serge-scl/braslet/design CAD/cup04.FCStd

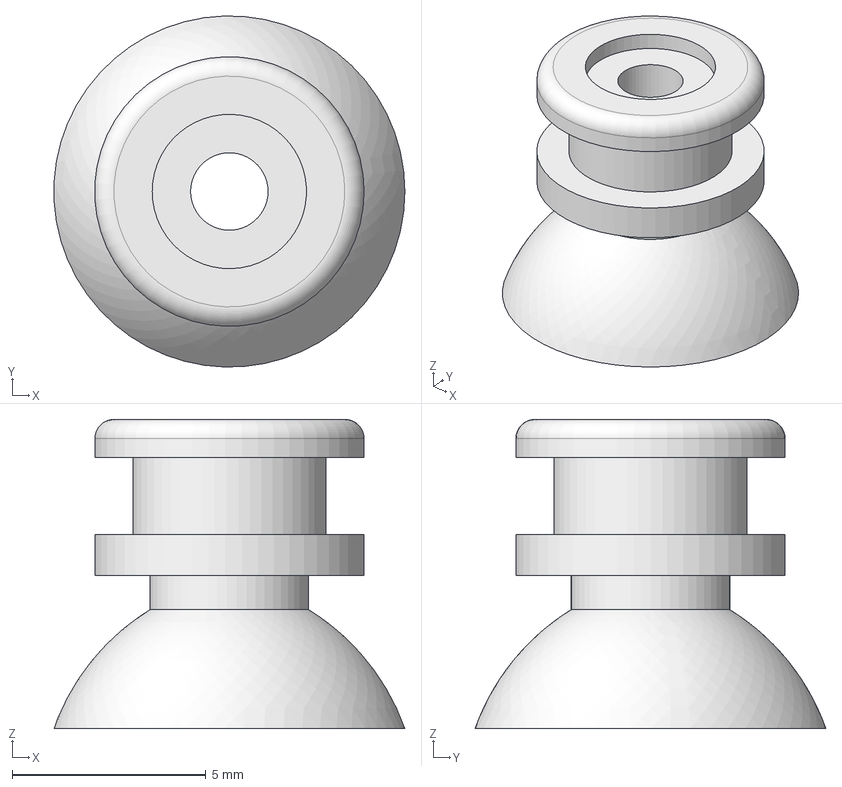
[picture p15: CAD file, 2022-11-26]
design CAD/cup04.FCStd
9.07 x 9.07 x 7.99 mm
