serge-scl/braslet/design CAD/sub_assembly/claster_feed_ring03.FCStd

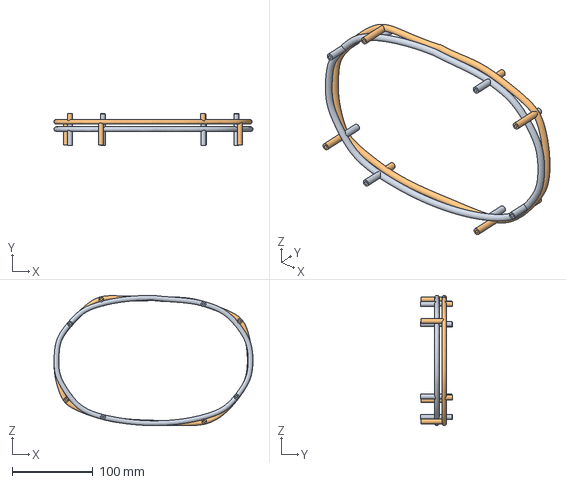
[picture p16: CAD file, 2022-08-05]
design CAD/sub_assembly/claster_feed_ring03.FCStd
246.3 x 39.1 x 161.5 mm
pip_feed_ring05_001
pip_feed_ring06_001
