serge-scl/braslet/design CAD/btm_spr_modl_sh03.FCStd

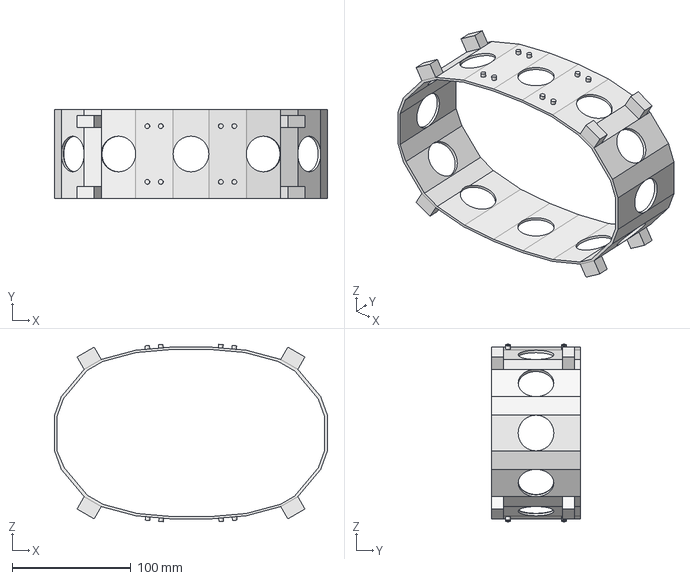
[picture p17: CAD file, 2022-10-20]
design CAD/btm_spr_modl_sh03.FCStd
230.0 x 75.0 x 149.6 mm
