serge-scl/braslet/design CAD/sub_assembly/con_spring_pip_sct01.FCStd

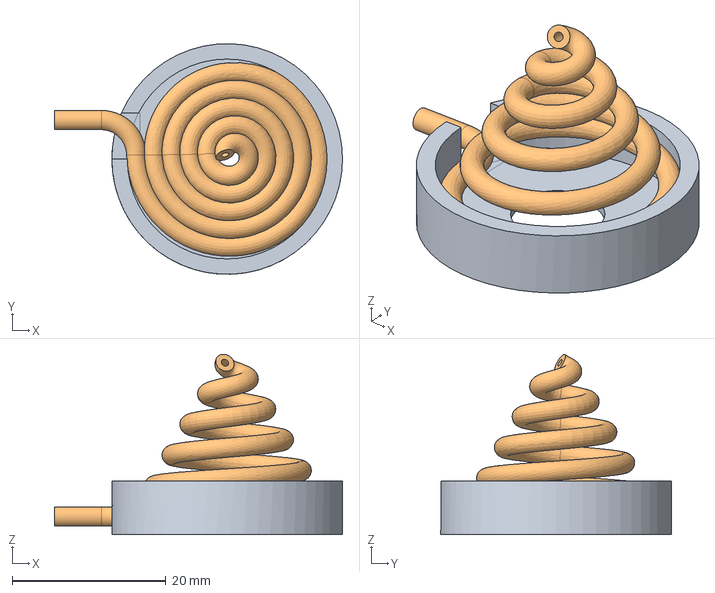
[picture p18: CAD file, 2022-07-16]
design CAD/sub_assembly/con_spring_pip_sct01.FCStd
37.5 x 30.0 x 23.5 mm
con_pip_spring_sokt01_001
con_spring_plp01_001
