serge-scl/braslet/design CAD/pip_feed_ring05.FCStd

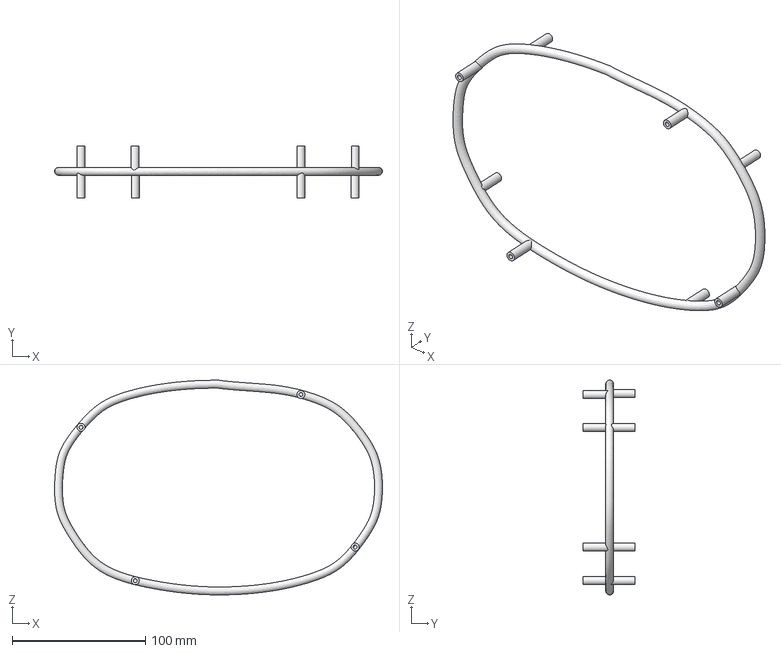
[picture p19: CAD file, 2022-08-05]
design CAD/pip_feed_ring05.FCStd
246.3 x 39.0 x 161.3 mm
