serge-scl/braslet/design CAD/sub_assembly/con_spring_sens_sct01.FCStd

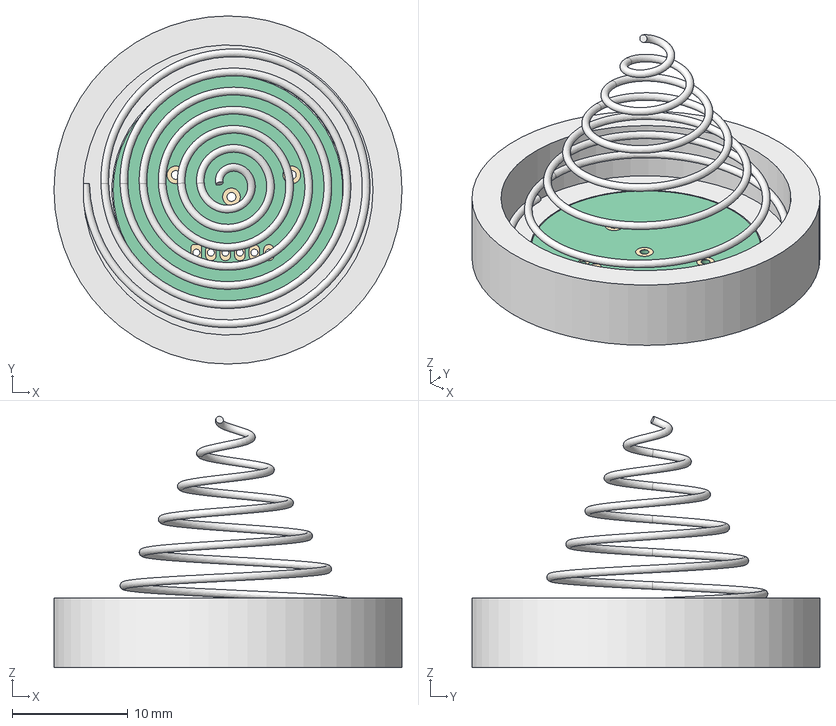
[picture p20: CAD file, 2022-07-15]
design CAD/sub_assembly/con_spring_sens_sct01.FCStd
30.0 x 30.0 x 21.7 mm
con_spring_sockt01_001
con_spring_stl01_001
Pcb_2f88
topPads_2f88
botPads_2f88
