serge-scl/braslet/design CAD/sub_assembly/solenoid_in_chamb01.FCStd

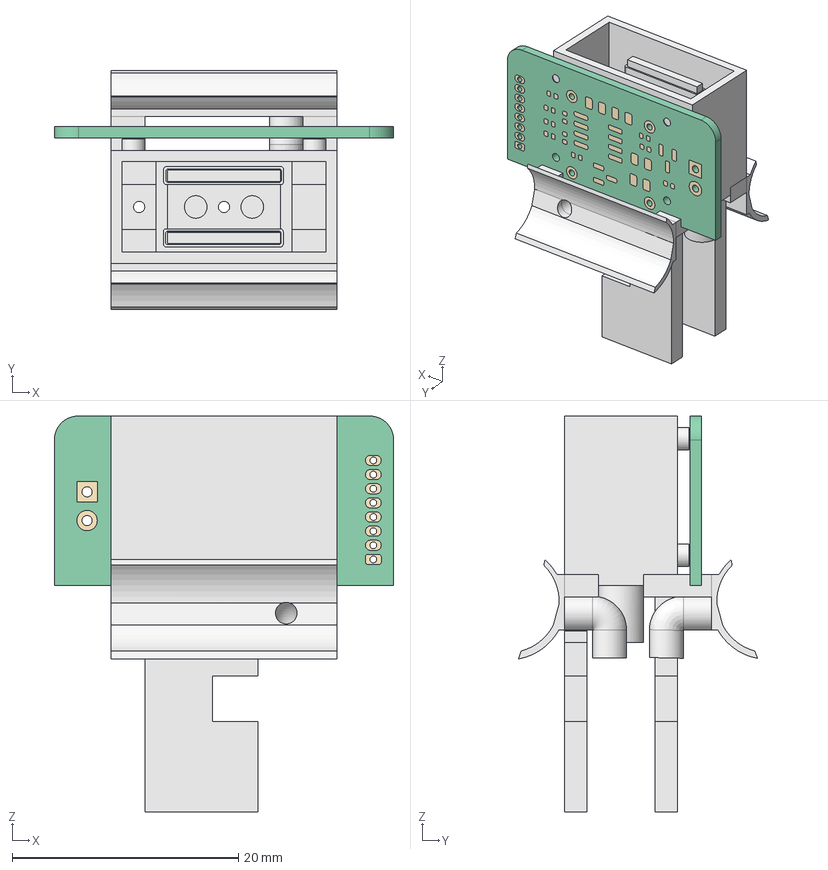
[picture p21: CAD file, 2022-07-13]
design CAD/sub_assembly/solenoid_in_chamb01.FCStd
30.0 x 21.1 x 35.0 mm
shell_chamb12_001
el_magnetcore03_001
magn_coil03_Body_001
magn_coil03_Body_002
Pcb_b2f7
topPads_b2f7
botPads_b2f7
actuator8_pistonPCBside_001
actuator8_piston_001
