serge-scl/braslet/design CAD/lips02.FCStd

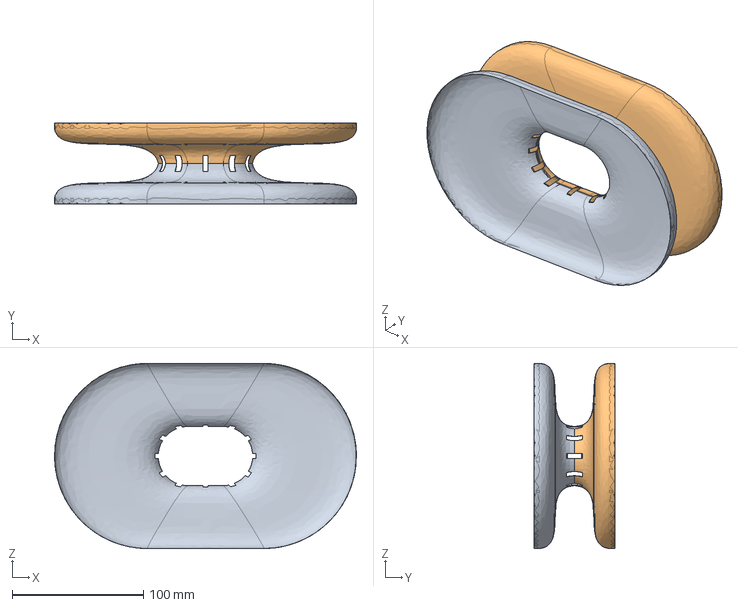
[picture p22: CAD file, 2022-07-19]
design CAD/lips02.FCStd
230.3 x 62.0 x 141.2 mm
Extrusion (Mirror #1)
