serge-scl/braslet/design CAD/sub_assembly/Ring_pneum_act01.FCStd

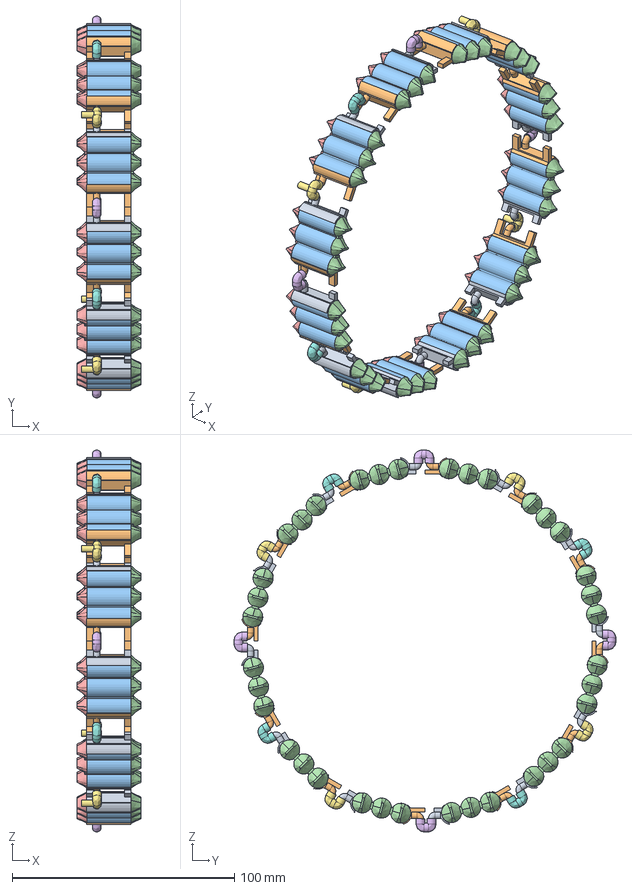
[picture p23: CAD file, 2022-05-03]
design CAD/sub_assembly/Ring_pneum_act01.FCStd
29.0 x 171.8 x 171.8 mm
