serge-scl/braslet/design CAD/con_pip_spring_sokt01.FCStd

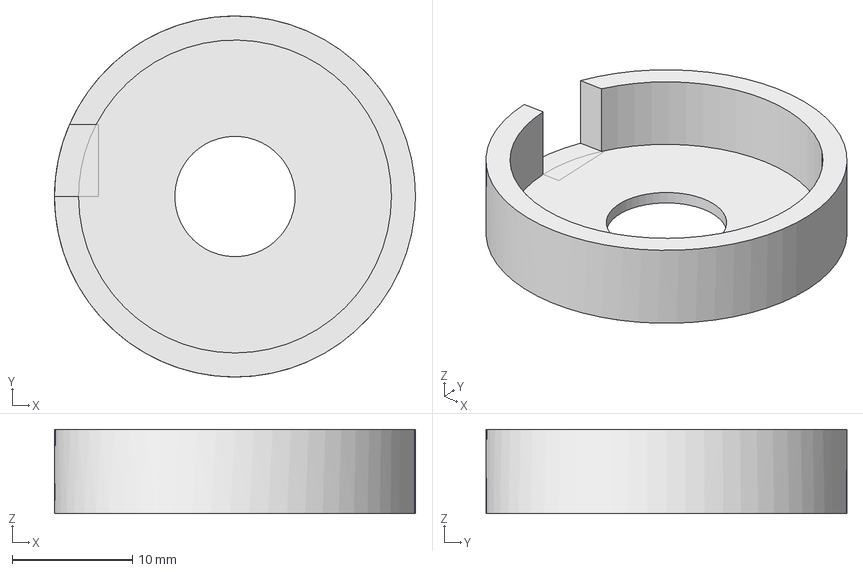
[picture p24: CAD file, 2022-07-16]
design CAD/con_pip_spring_sokt01.FCStd
30.0 x 30.0 x 7.00 mm
