serge-scl/braslet/design CAD/sub_assembly/ring_vacuum_line01.FCStd

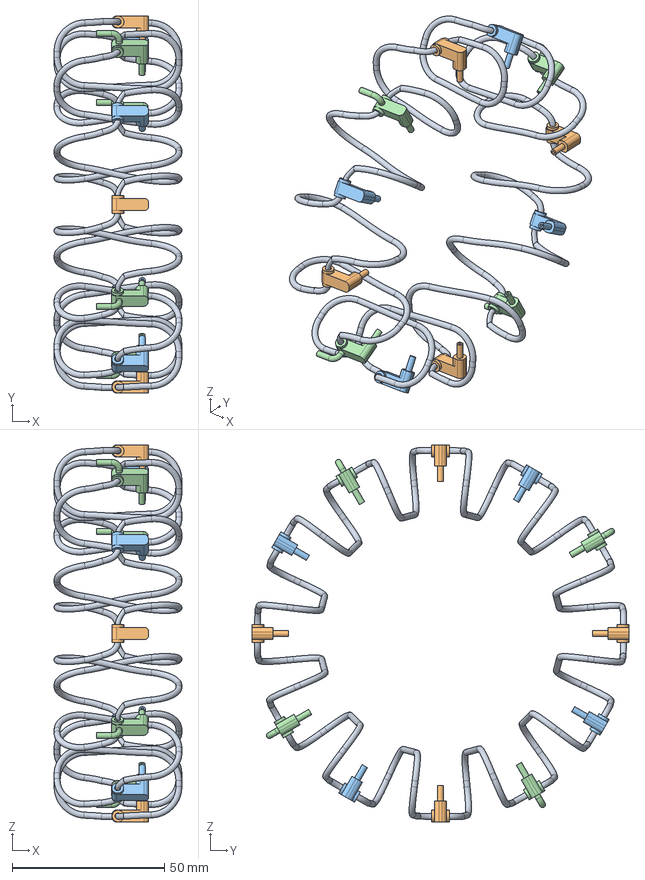
[picture p25: CAD file, 2022-04-30]
design CAD/sub_assembly/ring_vacuum_line01.FCStd
42.0 x 123.9 x 123.9 mm
