serge-scl/braslet/design CAD/con_spring_sockt01.FCStd

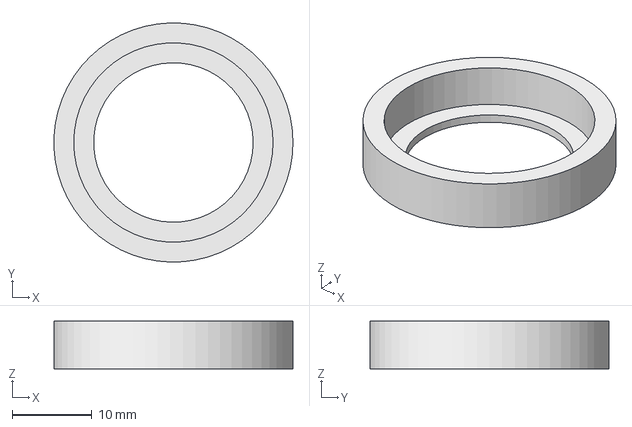
[picture p26: CAD file, 2022-07-15]
design CAD/con_spring_sockt01.FCStd
30.0 x 30.0 x 6.00 mm
