serge-scl/braslet/design CAD/con_spring_plp01.FCStd

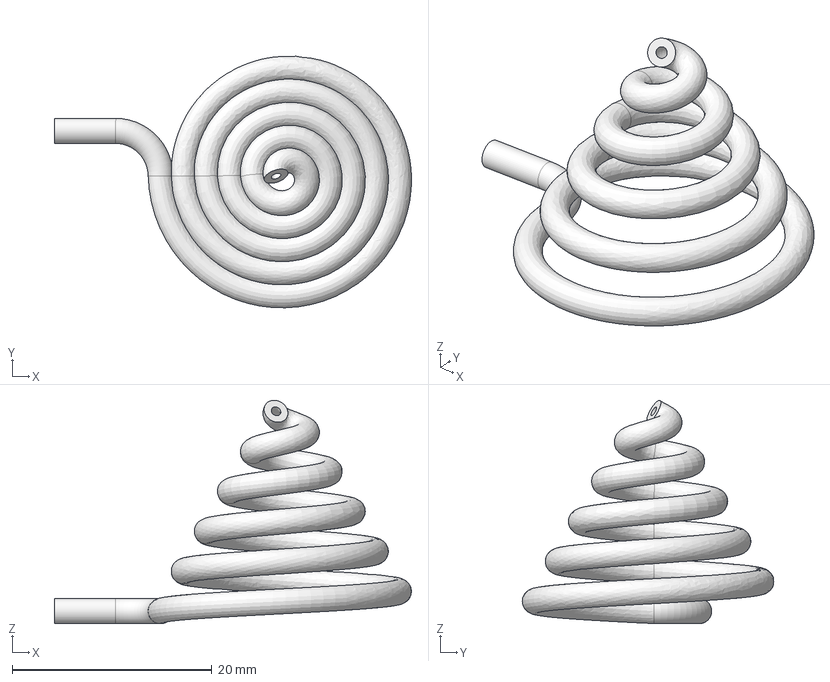
[picture p27: CAD file, 2022-07-13]
design CAD/con_spring_plp01.FCStd
35.7 x 25.2 x 22.3 mm
