serge-scl/braslet/design CAD/con_spring_stl01.FCStd

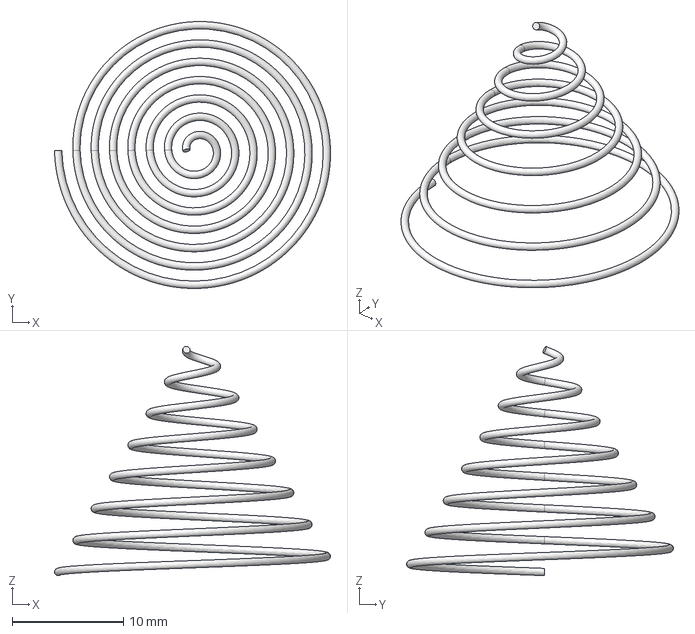
[picture p28: CAD file, 2022-07-13]
design CAD/con_spring_stl01.FCStd
24.8 x 24.0 x 20.6 mm
