serge-scl/braslet/design CAD/top_spr_modl_shell01.FCStd

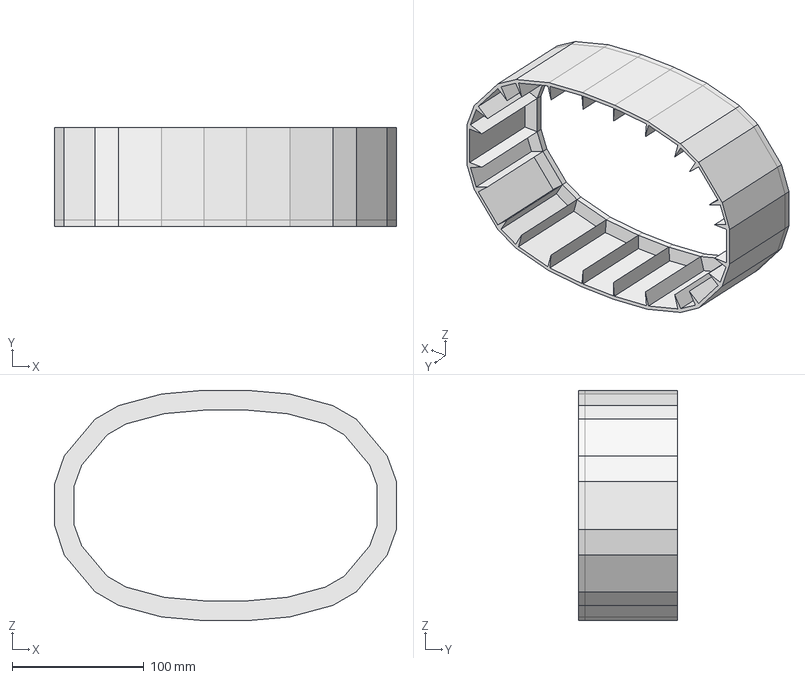
[picture p29: CAD file, 2022-07-08]
design CAD/top_spr_modl_shell01.FCStd
259.6 x 75.0 x 175.0 mm
