serge-scl/braslet/design CAD/coil_pins02.FCStd

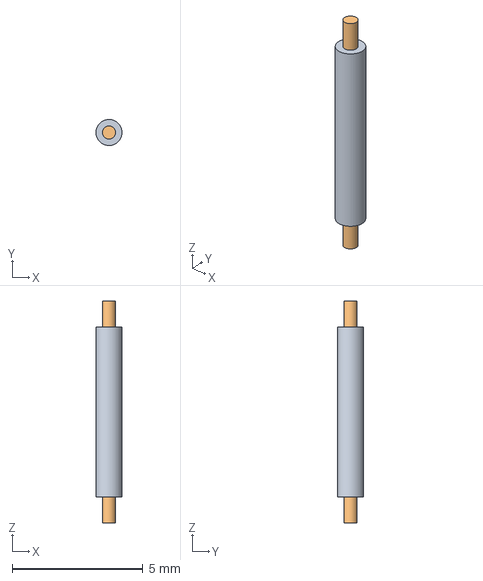
[picture p30: CAD file, 2022-05-10]
design CAD/coil_pins02.FCStd
0.999 x 1 x 8.50 mm
Tube
