serge-scl/braslet/design CAD/coil_pins01.FCStd

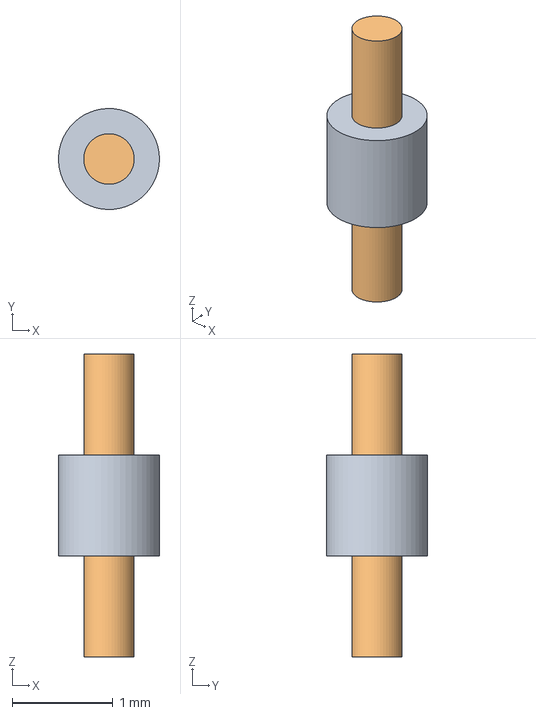
[picture p31: CAD file, 2022-05-10]
design CAD/coil_pins01.FCStd
0.999 x 1 x 3.00 mm
Tube
