serge-scl/braslet/design CAD/branch_pipe_tee0_feeder01.FCStd

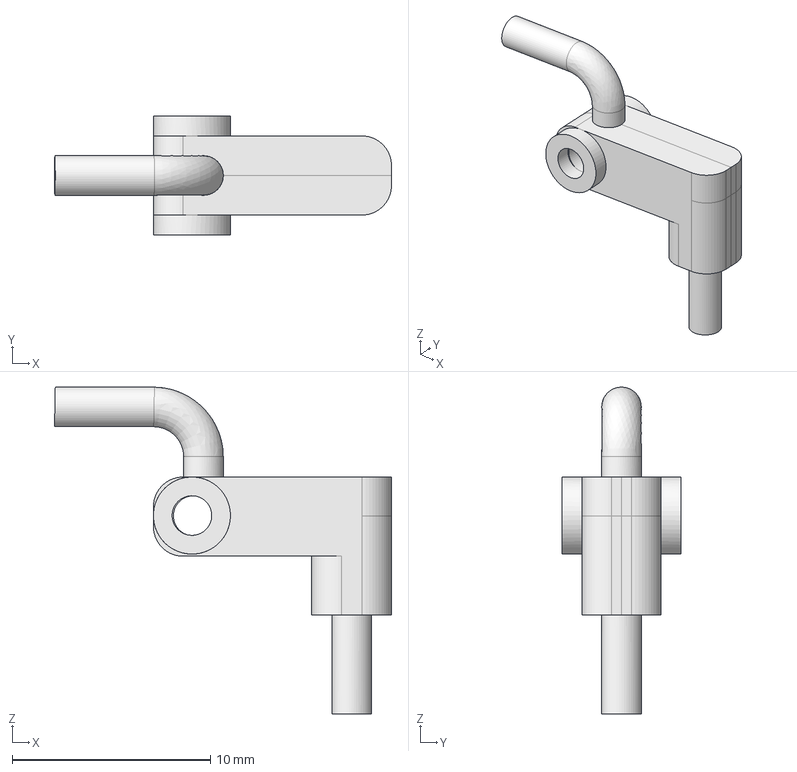
[picture p32: CAD file, 2022-04-24]
design CAD/branch_pipe_tee0_feeder01.FCStd
17.0 x 6.00 x 16.5 mm
