serge-scl/braslet/design CAD/bush_feeder03.FCStd

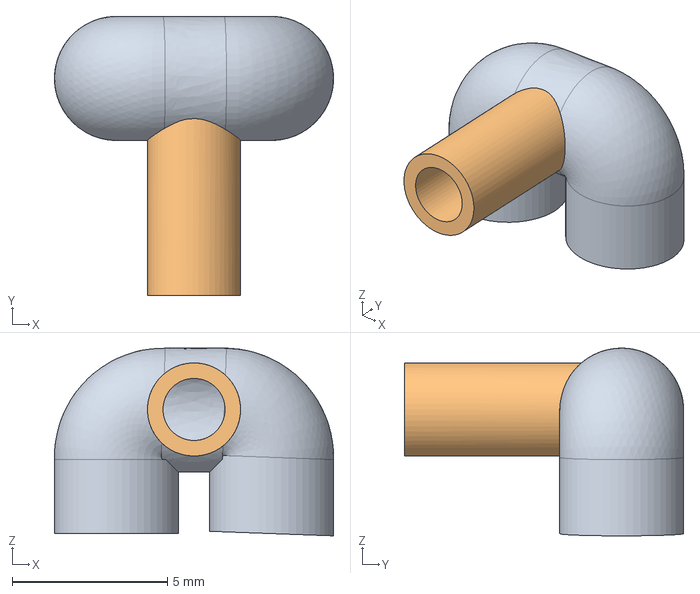
[picture p33: CAD file, 2022-04-21]
design CAD/bush_feeder03.FCStd
8.99 x 9.00 x 6.05 mm
