serge-scl/braslet/design CAD/magn_coil03.FCStd

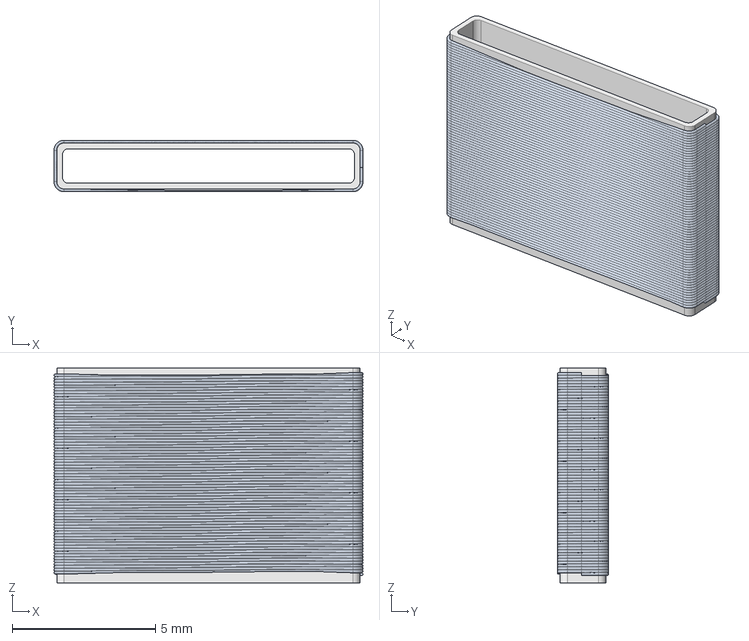
[picture p34: CAD file, 2022-04-20]
design CAD/magn_coil03.FCStd
10.8 x 1.80 x 7.50 mm
