serge-scl/braslet/design CAD/bush_simply02.FCStd

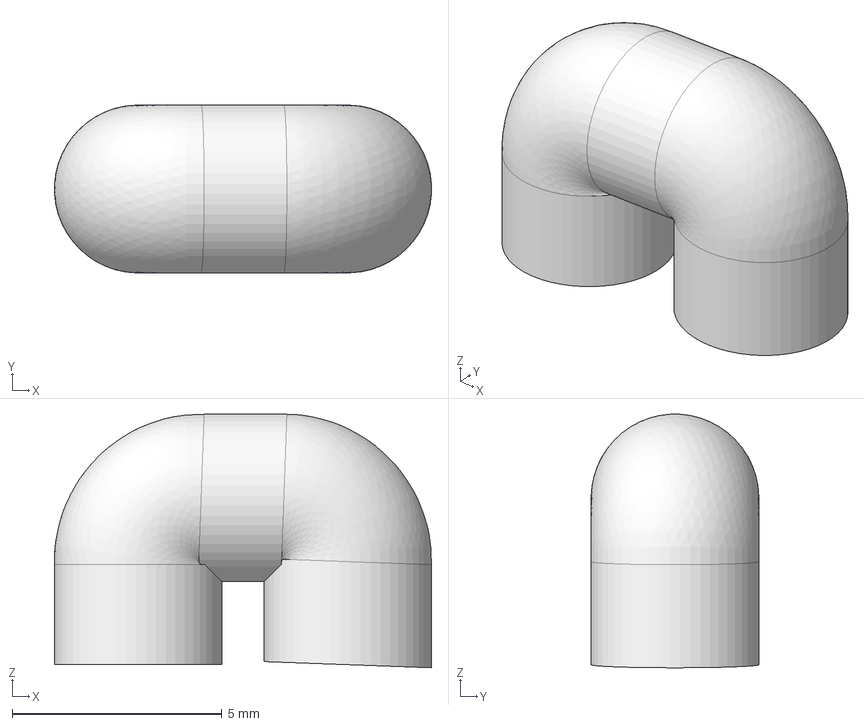
[picture p35: CAD file, 2022-04-19]
design CAD/bush_simply02.FCStd
8.99 x 4.00 x 6.05 mm
