serge-scl/braslet/design CAD/frame_spring03.FCStd

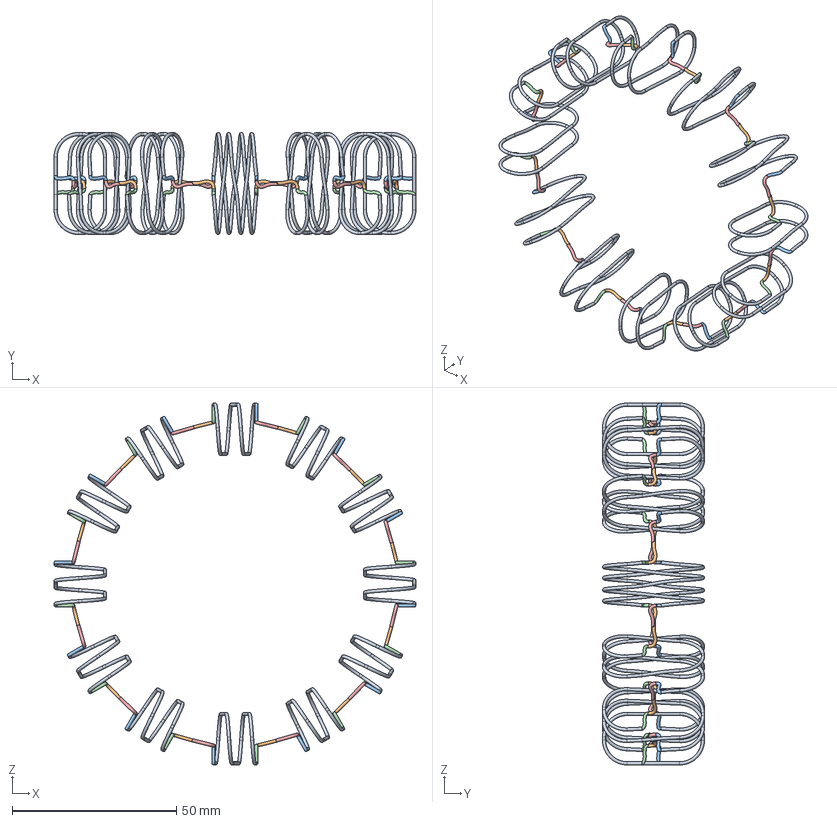
[picture p36: CAD file, 2022-04-10]
design CAD/frame_spring03.FCStd
110.0 x 31.0 x 110.0 mm
