serge-scl/braslet/design CAD/branch_pipe_tee01.FCStd

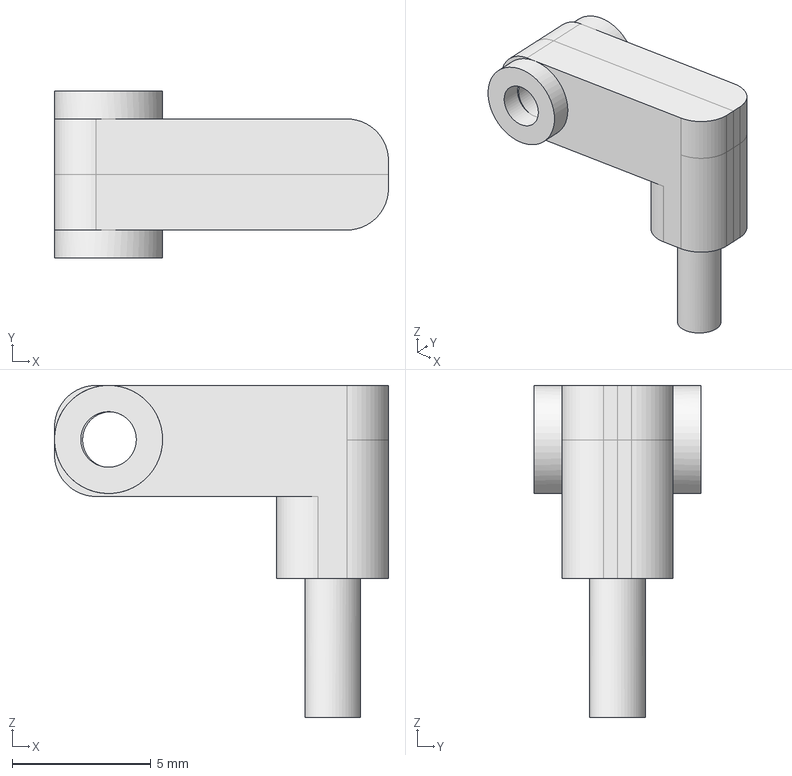
[picture p37: CAD file, 2022-04-06]
design CAD/branch_pipe_tee01.FCStd
12.0 x 6.00 x 12.0 mm
