serge-scl/braslet/design CAD/vacuum_pip_ell04.FCStd

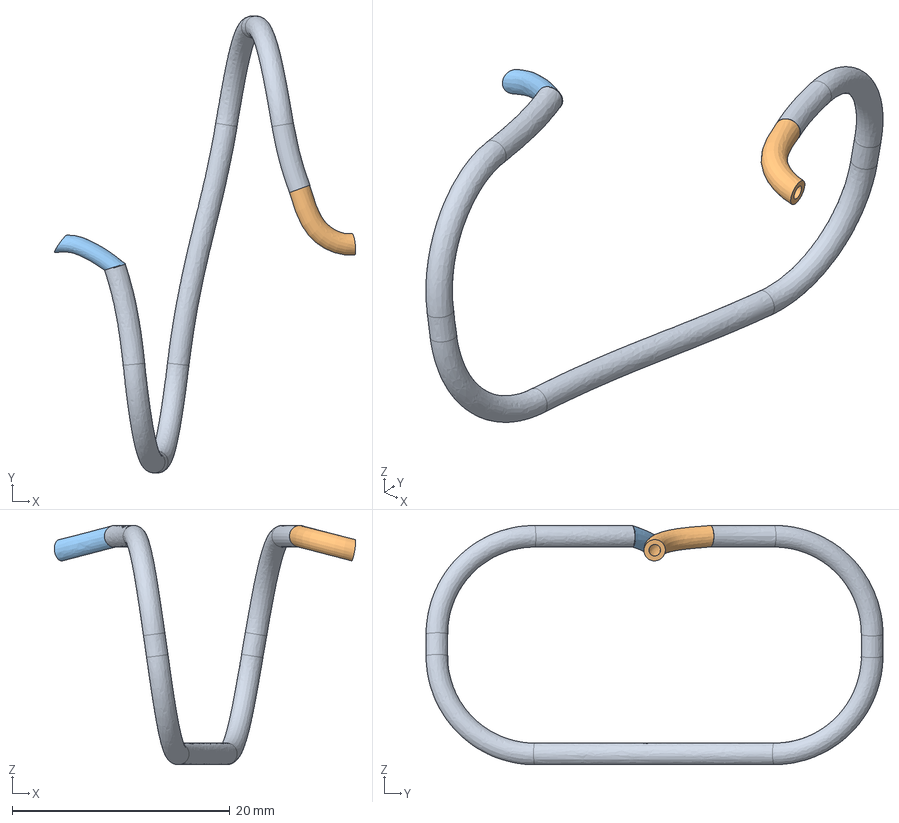
[picture p38: CAD file, 2022-04-01]
design CAD/vacuum_pip_ell04.FCStd
27.7 x 42.0 x 22.0 mm
