serge-scl/braslet/design CAD/actuator8_side.FCStd

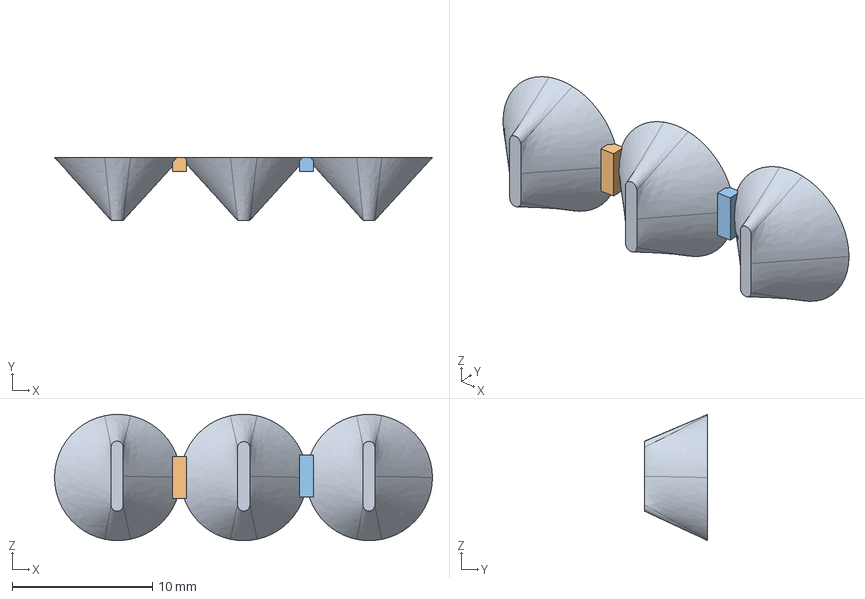
[picture p39: CAD file, 2022-03-10]
design CAD/actuator8_side.FCStd
27.0 x 4.50 x 9.03 mm
