serge-scl/braslet/design CAD/actuator8.FCStd

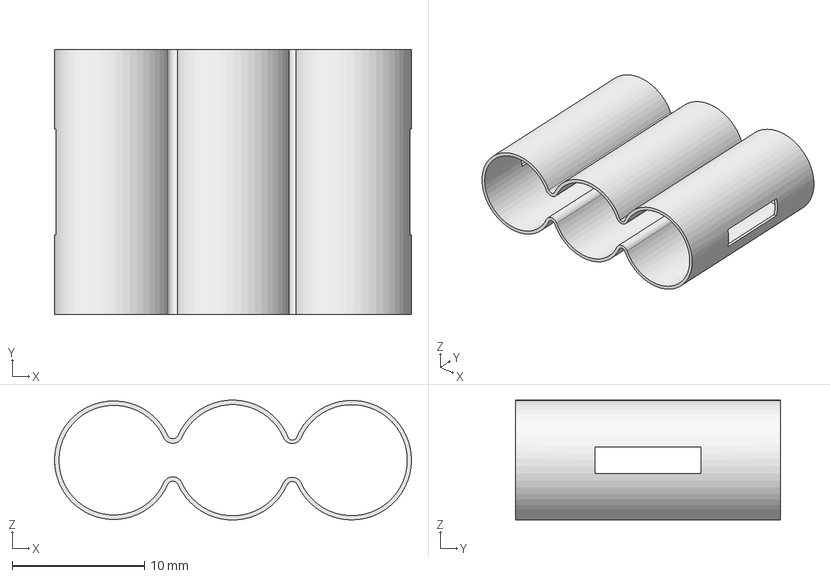
[picture p40: CAD file, 2022-03-08]
design CAD/actuator8.FCStd
27.0 x 20.0 x 9.06 mm
