serge-scl/braslet/design CAD/valve_slide01.FCStd

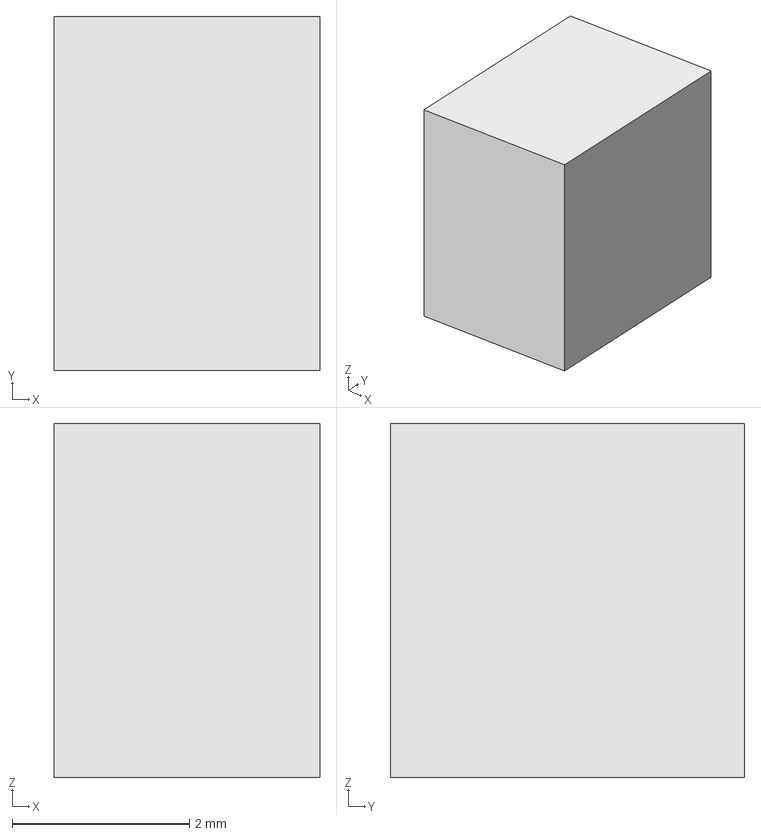
[picture p41: CAD file, 2022-03-06]
design CAD/valve_slide01.FCStd
3.00 x 4.00 x 4.00 mm
