serge-scl/braslet/design CAD/pin_spring_fix01.FCStd

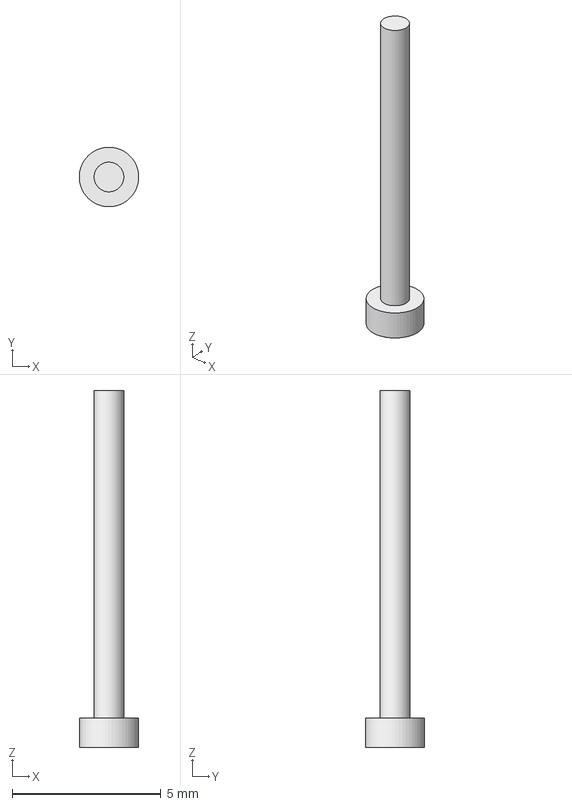
[picture p42: CAD file, 2022-02-27]
design CAD/pin_spring_fix01.FCStd
2.00 x 2.00 x 12.0 mm
