serge-scl/braslet/design CAD/el_magnetcore03.FCStd

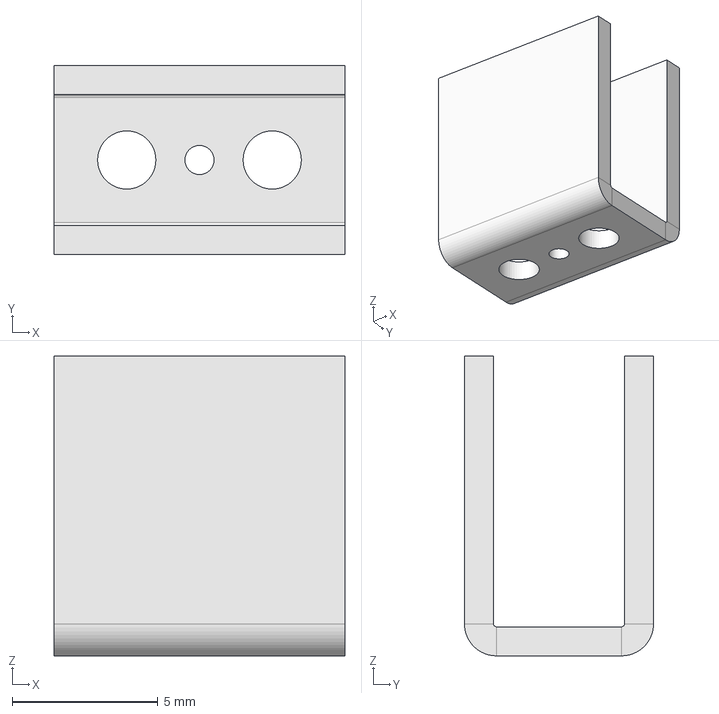
[picture p43: CAD file, 2022-02-26]
design CAD/el_magnetcore03.FCStd
10.0 x 6.50 x 10.3 mm
