serge-scl/braslet/design CAD/spring_stop_01.FCStd

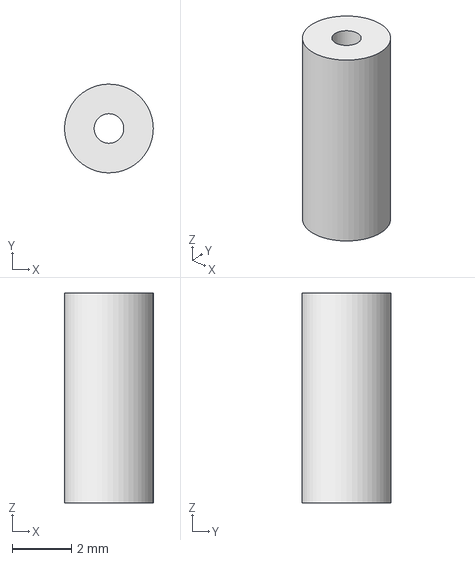
[picture p44: CAD file, 2022-02-26]
design CAD/spring_stop_01.FCStd
3.00 x 3.00 x 7.10 mm
